Emrecanbl/ESP32_Power_Meter/Firmware/Platformio/ESP32_Powermeter/include/Web_Ui.h

// Load required libraries
#include <WiFi.h>
#include <WebServer.h>

void WEB_UI_init();
void WEB_UI_Stream(PowerSample &Power_Values);
void handle_OnConnect();
void handle_NotFound();
void handleEnergyCmd();
String createHTML();
